solderdev/wakeuplight_v2/wakeuplightv2/src/Storage.cpp

#include "Storage.hpp"

std::mutex preferences_lock;

// class Storage
// {
// private:
//   /* data */
// public:
//   Storage(/* args */);
//   ~Storage();
// };

// Storage::Storage(/* args */)
// {
// }

// Storage::~Storage()
// {
// }
